r0oland/bioterio/firmware_2022/include/secrets.h

#define SECRET_SSID "Kassiopeia"                                // replace MySSID with your WiFi network name
#define SECRET_PASS "SternbilddesNordhimmels"                            // replace MyPassword with your WiFi password

const char* ssid = "Kassiopeia";
const char* password = "SternbilddesNordhimmels";

const char* WIFI_SSID = "Kassiopeia";
const char* WIFI_PWD = "SternbilddesNordhimmels";
